DLLSTART/InstaFreeHeart/mechanical/openscad/out/ergonomics_overview.png

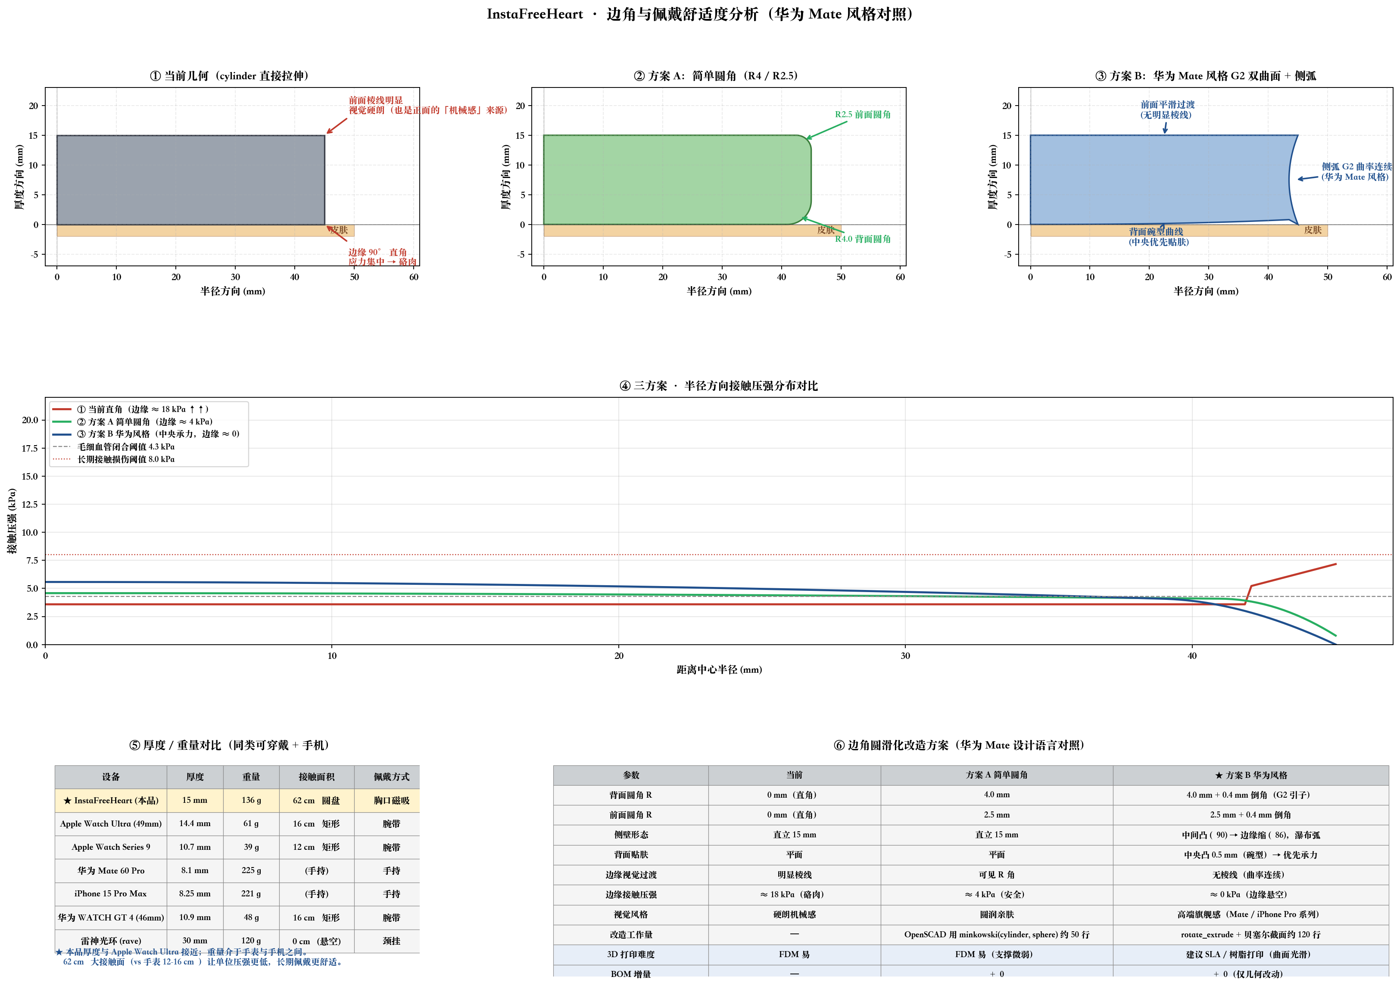
mechanical/openscad/out/ergonomics_overview.png
