DLLSTART/InstaFreeHeart/mechanical/openscad/out/power_modes.png

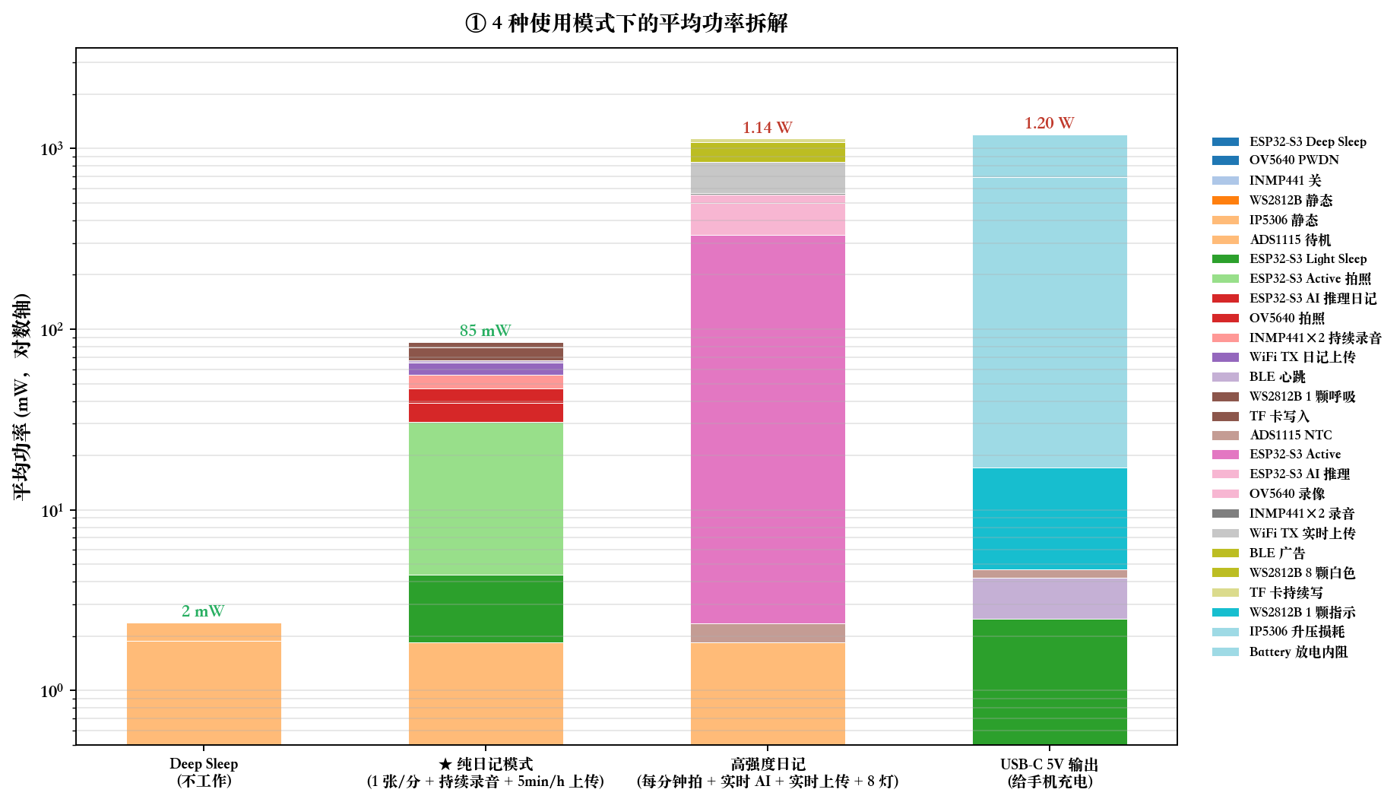
mechanical/openscad/out/power_modes.png
