DLLSTART/InstaFreeHeart/mechanical/openscad/out/power_overview.png

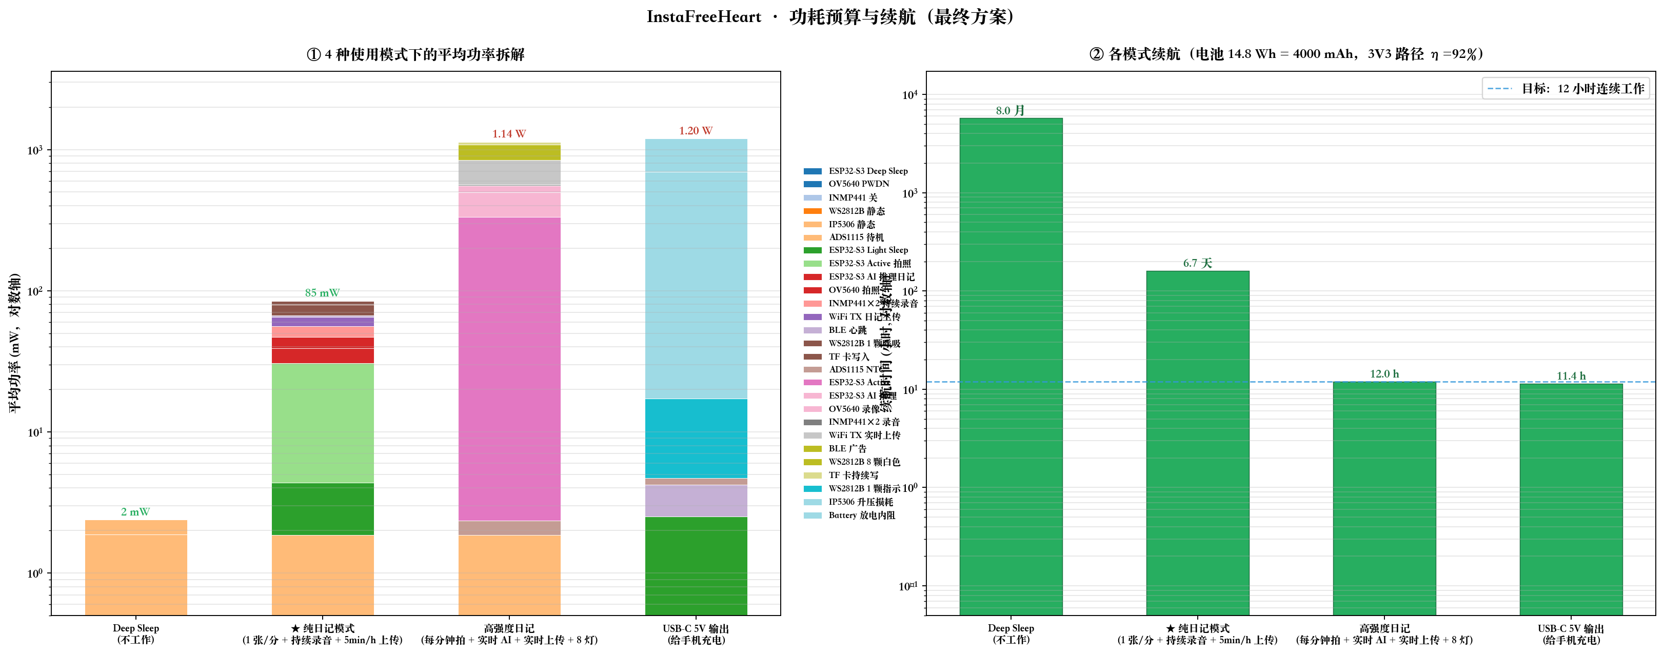
mechanical/openscad/out/power_overview.png
