DLLSTART/InstaFreeHeart/mechanical/openscad/out/preview_overview.png

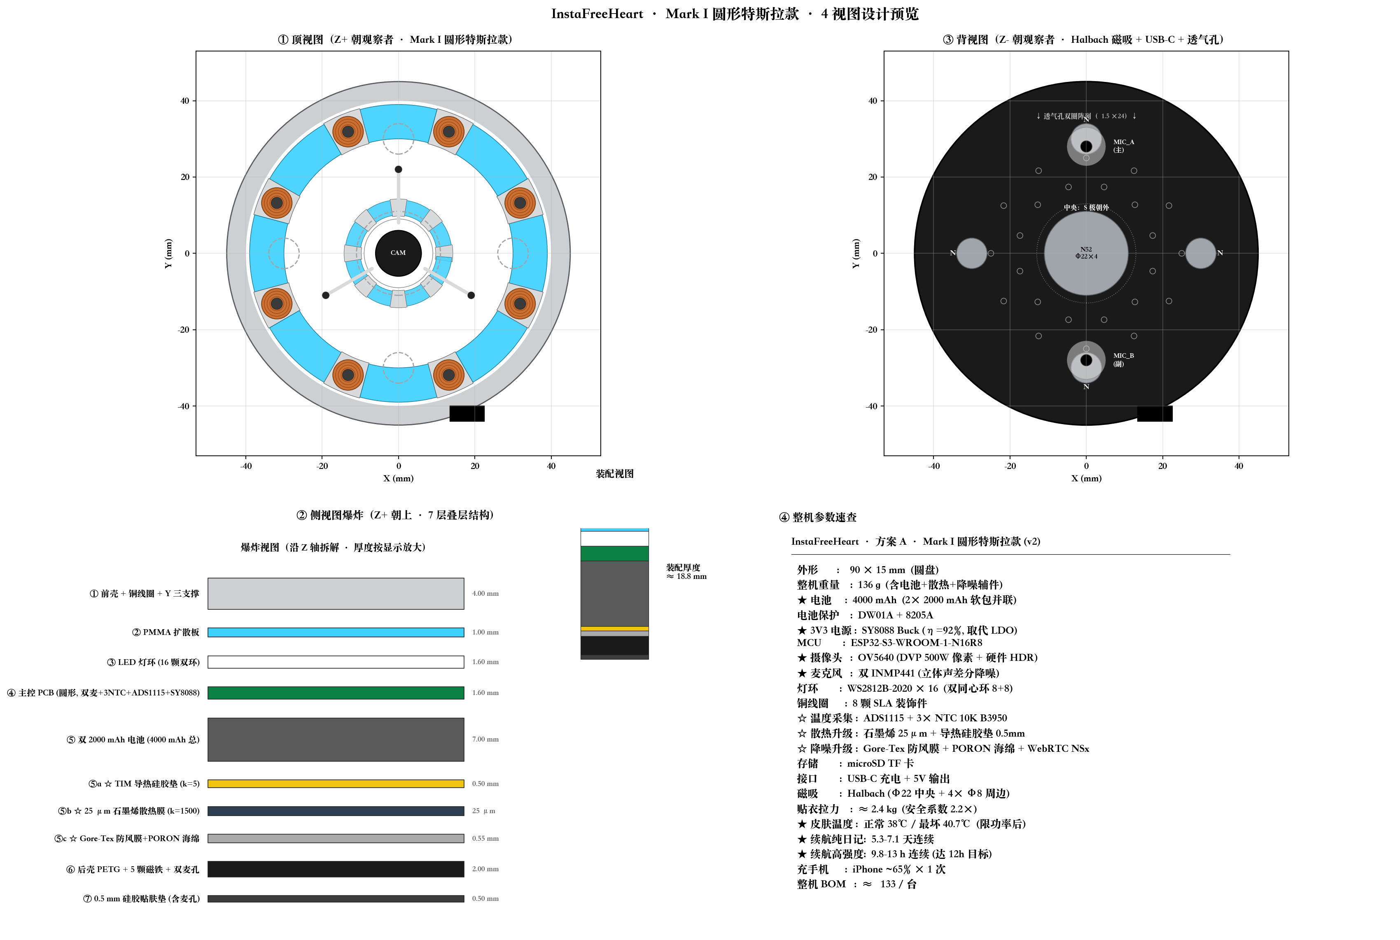
mechanical/openscad/out/preview_overview.png
