DLLSTART/InstaFreeHeart/mechanical/openscad/out/preview_top.png

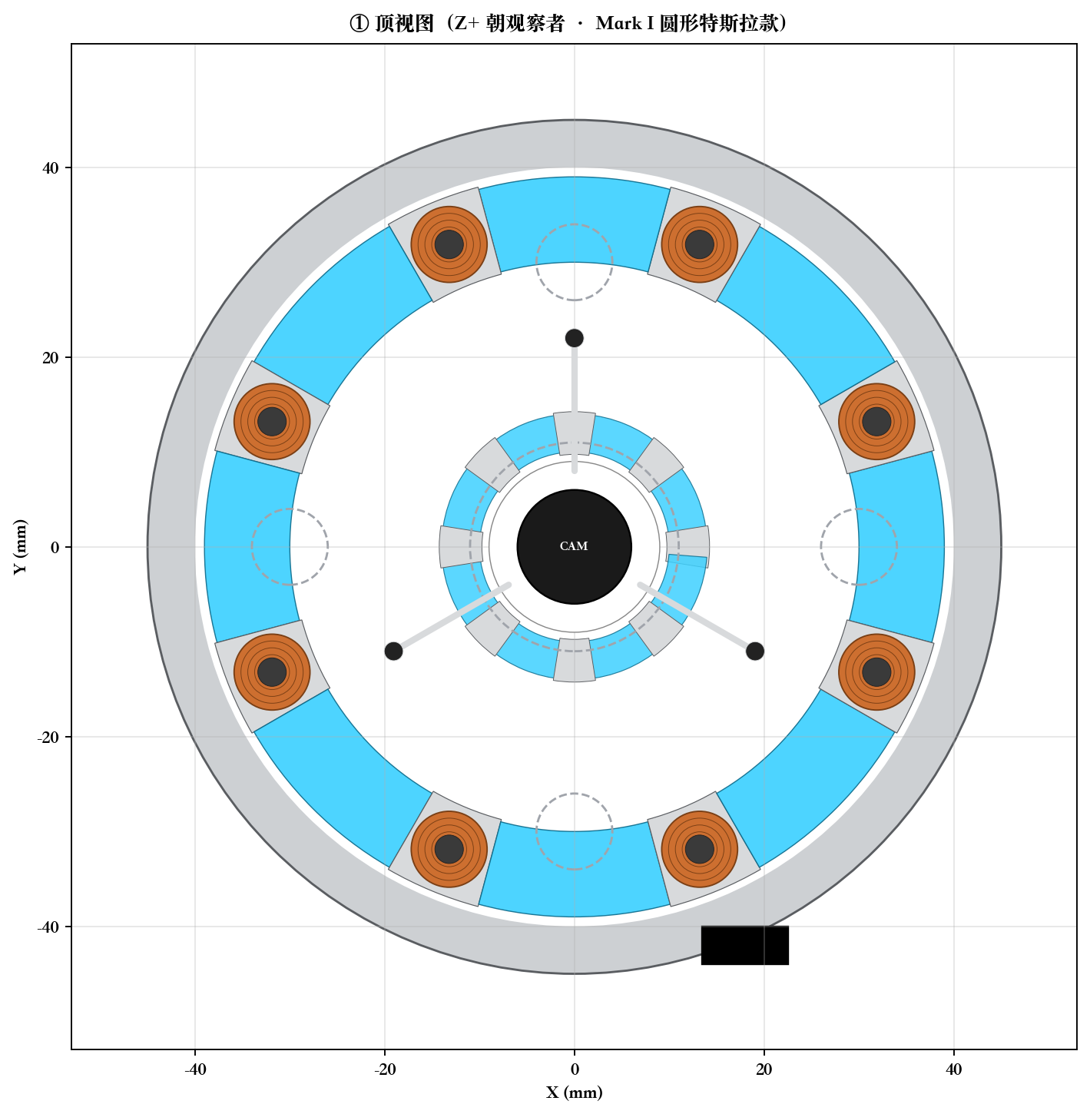
mechanical/openscad/out/preview_top.png
