DLLSTART/InstaFreeHeart/mechanical/openscad/out/render_back.png

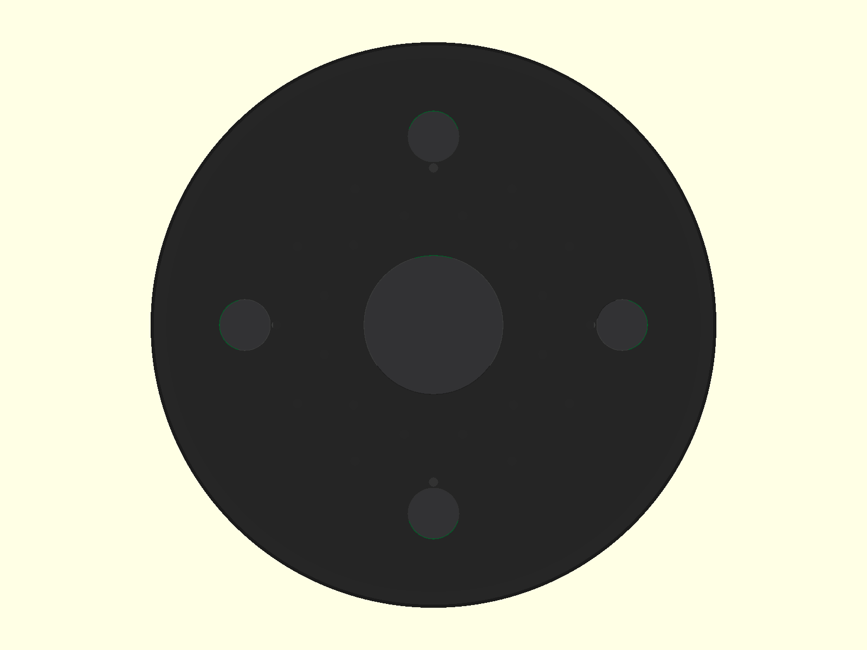
mechanical/openscad/out/render_back.png
