DLLSTART/InstaFreeHeart/mechanical/openscad/out/render_explode.png

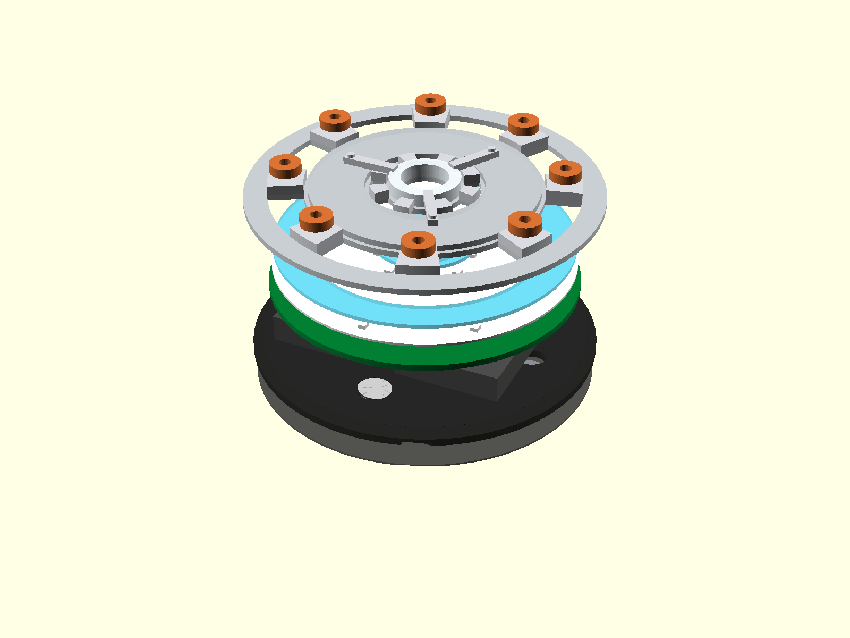
mechanical/openscad/out/render_explode.png
