DLLSTART/InstaFreeHeart/mechanical/openscad/out/render_iso.png

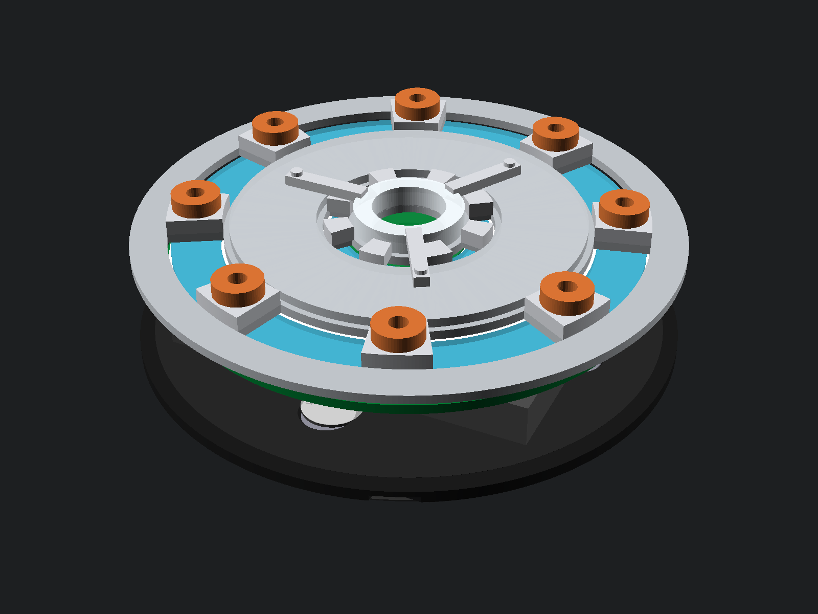
mechanical/openscad/out/render_iso.png
