DLLSTART/InstaFreeHeart/mechanical/openscad/out/render_overview_4view.png

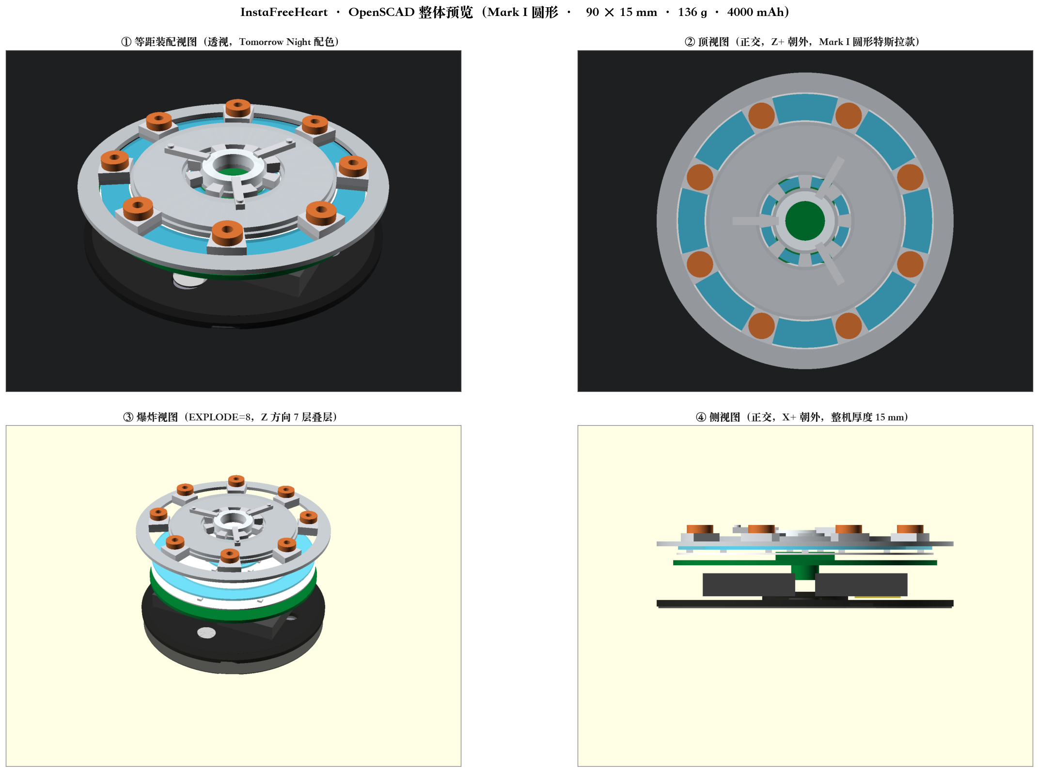
mechanical/openscad/out/render_overview_4view.png
