DLLSTART/InstaFreeHeart/mechanical/openscad/out/thermal_network.png

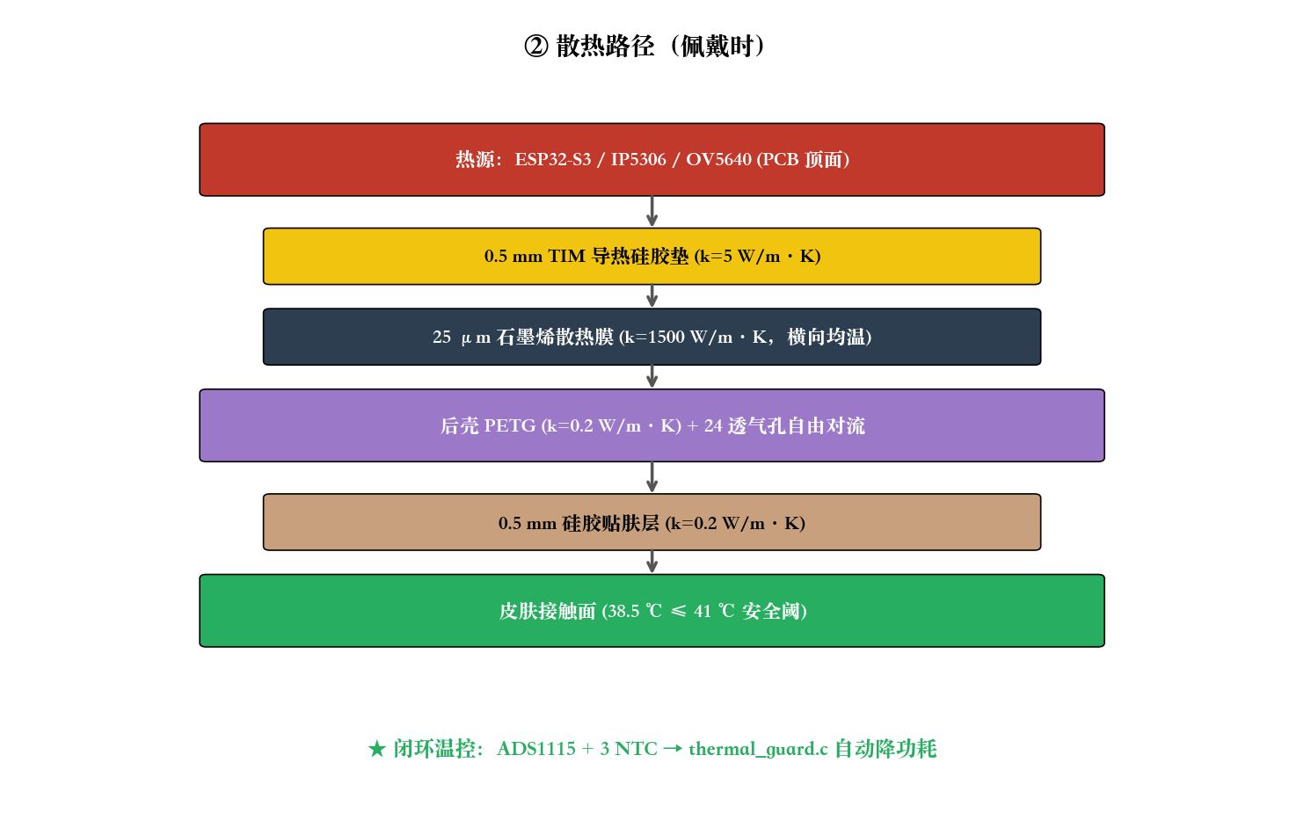
mechanical/openscad/out/thermal_network.png
