DLLSTART/InstaFreeHeart/mechanical/openscad/out/thermal_powers.png

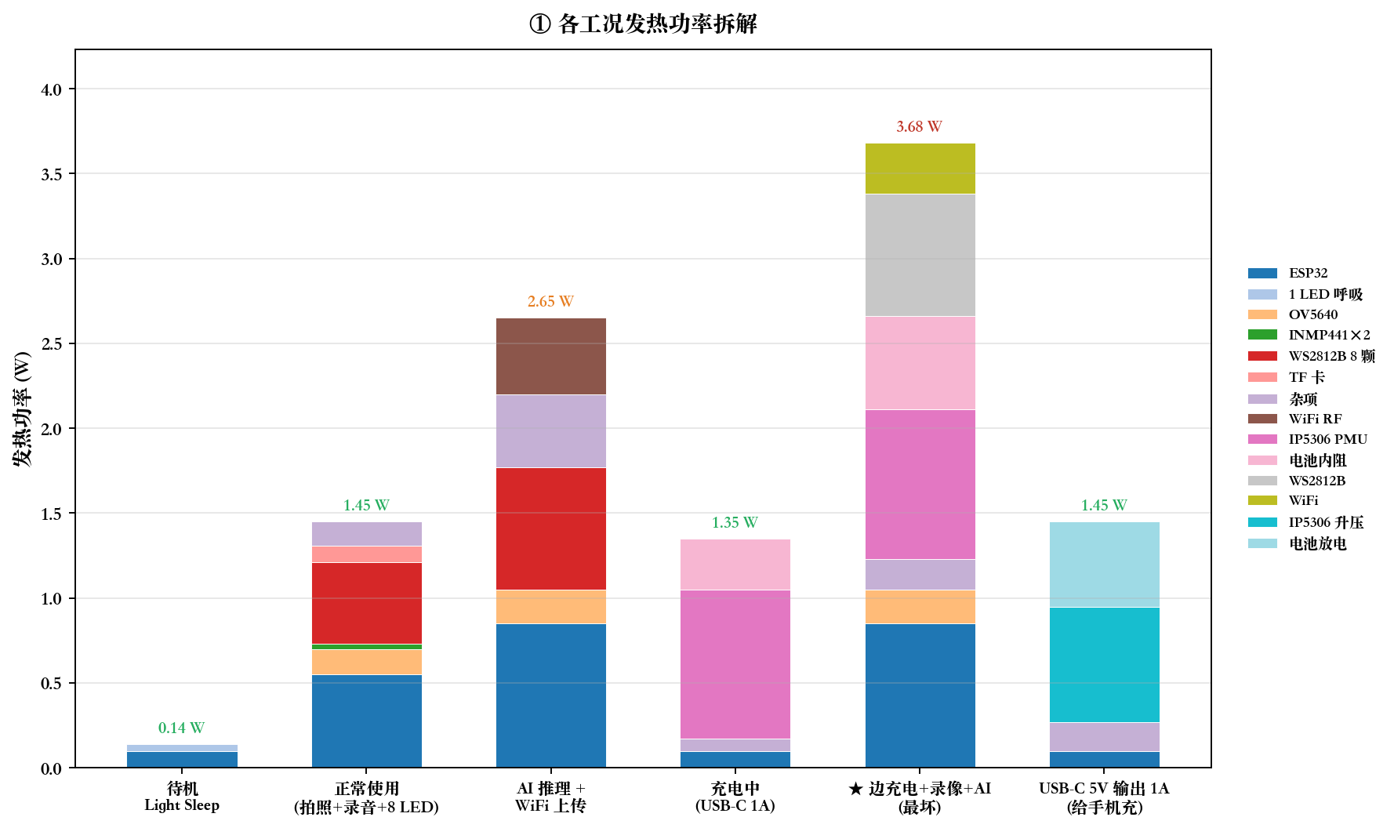
mechanical/openscad/out/thermal_powers.png
