DLLSTART/InstaFreeHeart/mechanical/openscad/out/thermal_temperatures.png

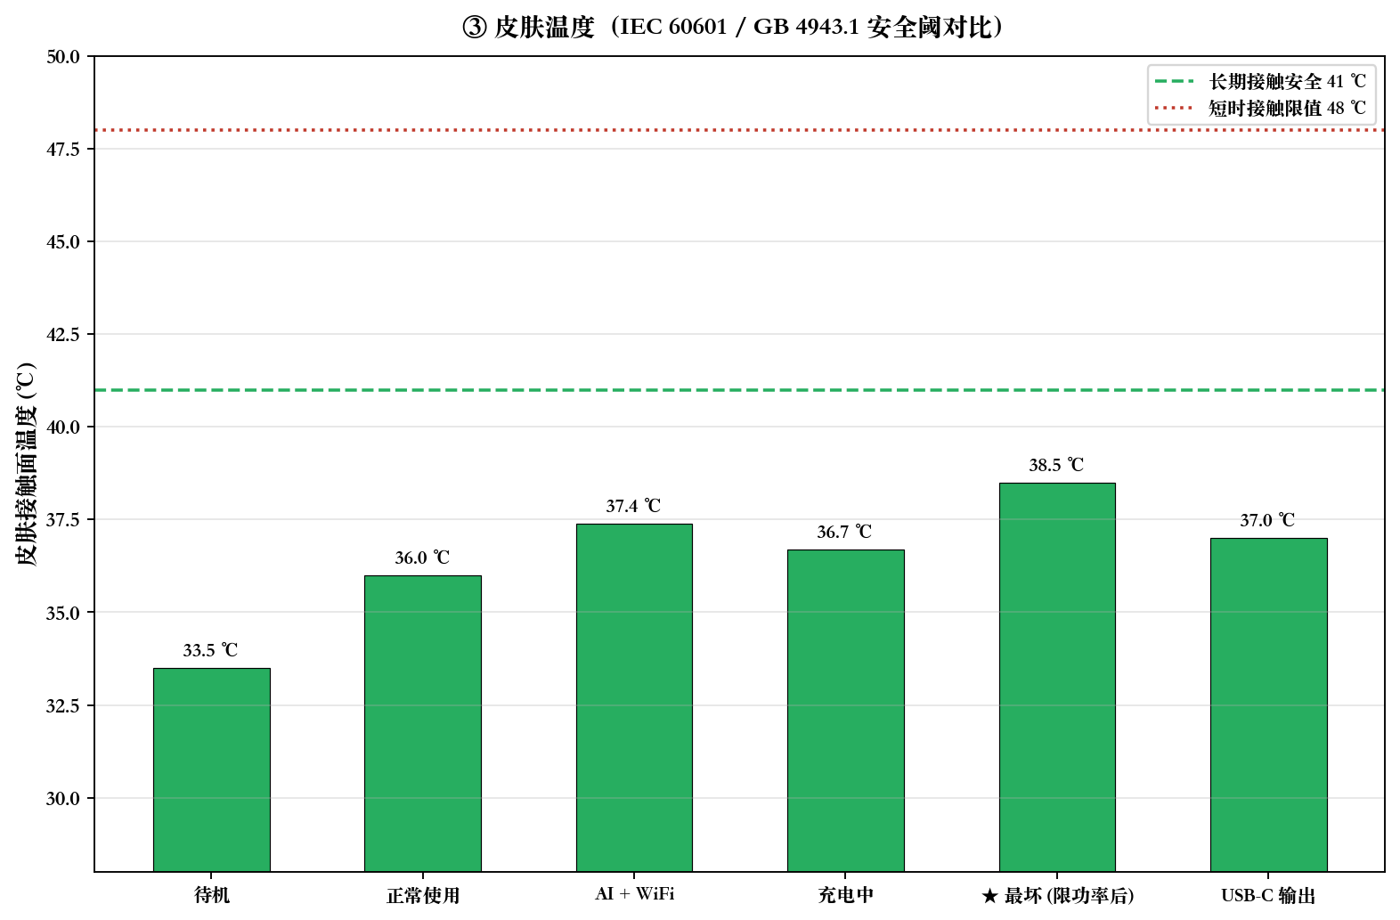
mechanical/openscad/out/thermal_temperatures.png
