DLLSTART/InstaFreeHeart/mechanical/openscad/out/preview_parts.png

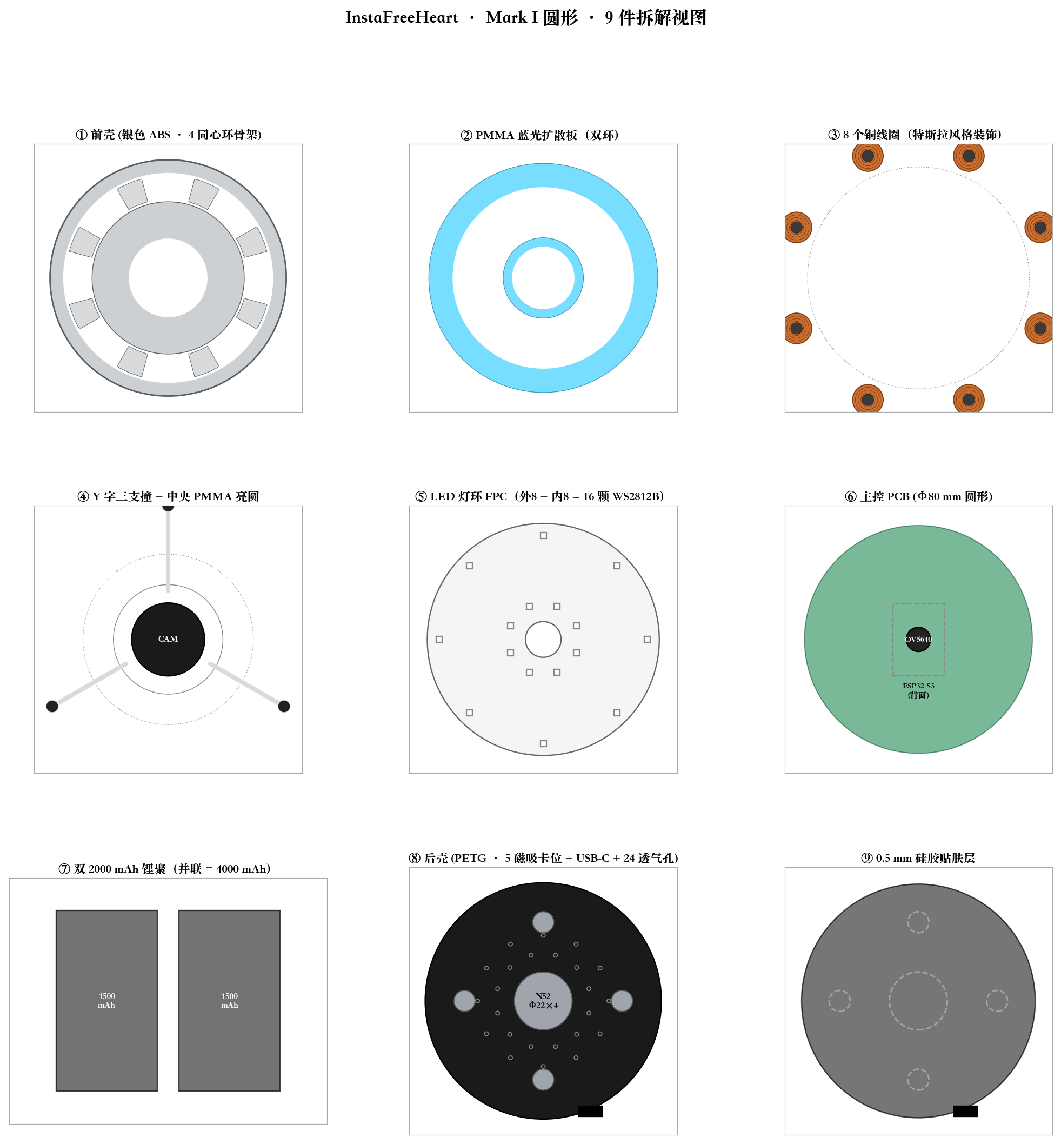
mechanical/openscad/out/preview_parts.png
